andreaskuster/igem19-ethz-phage-hw-model/model/growth_rate_regression.png

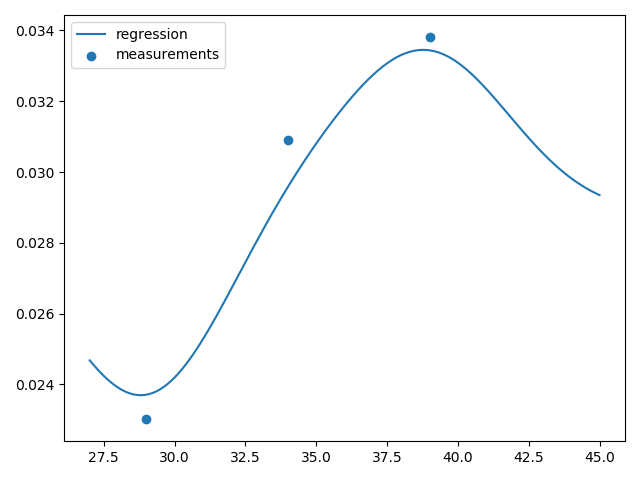
model/growth_rate_regression.png
