andreaskuster/igem19-ethz-phage-hw-model/recombineering/graphs.png

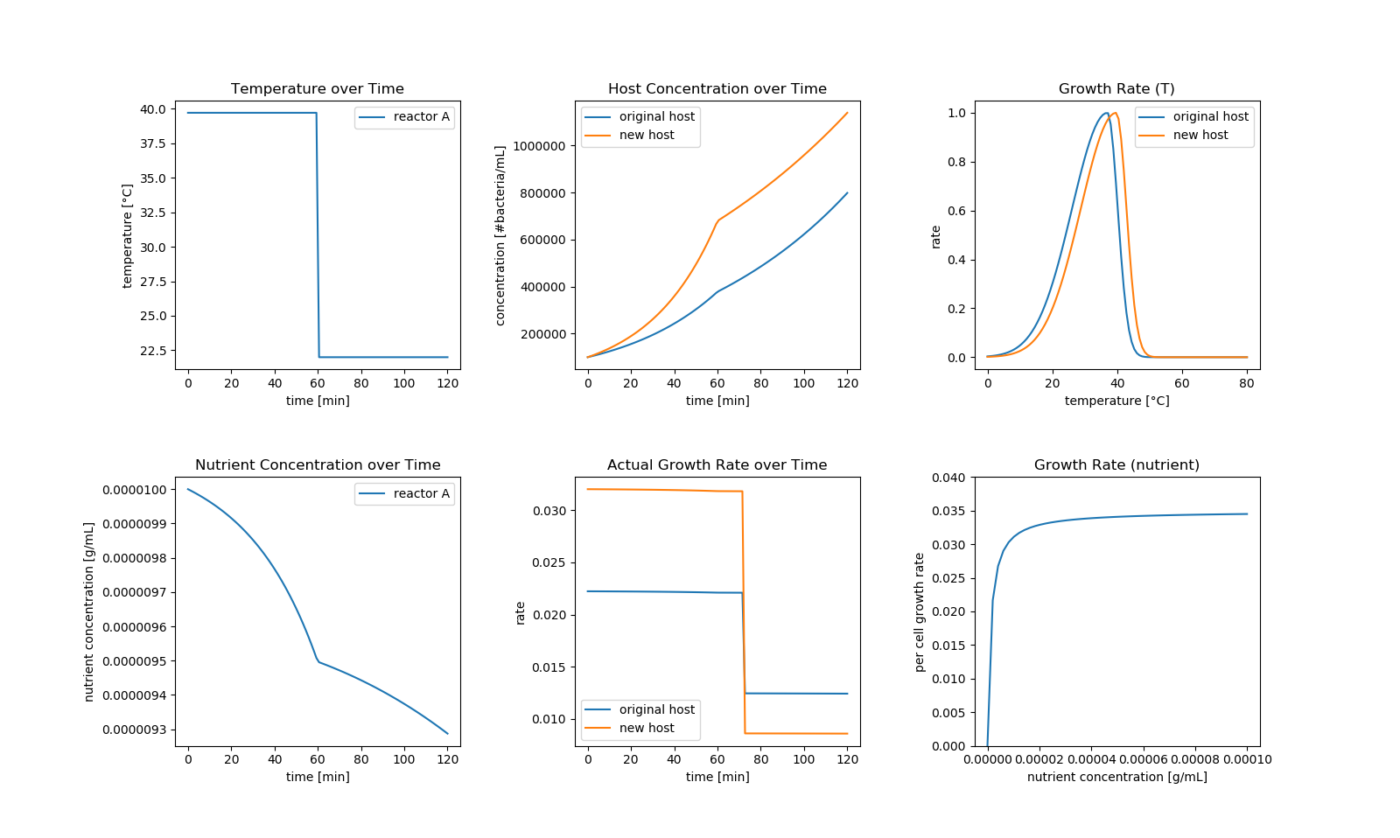
recombineering/graphs.png
